plinkysynth/plinky_public/sw/emu/plinkycenter.png

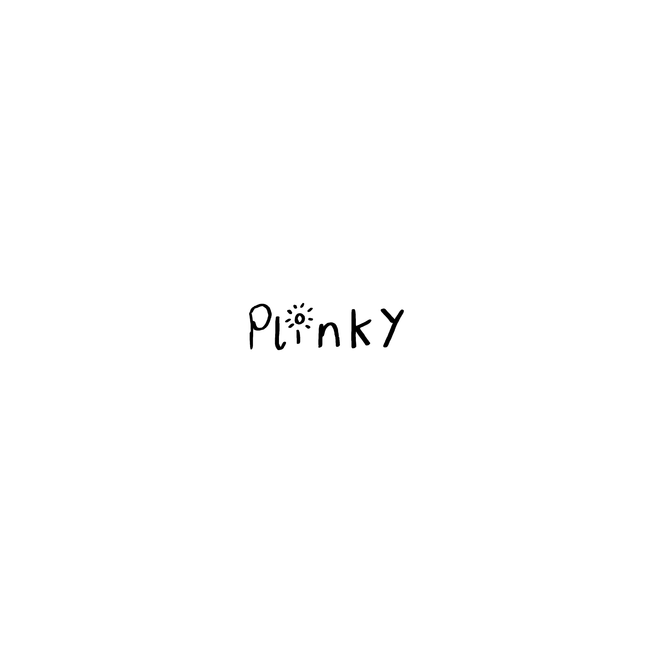
sw/emu/plinkycenter.png
