plinkysynth/plinky_public/sw/emu/plinkydots.png

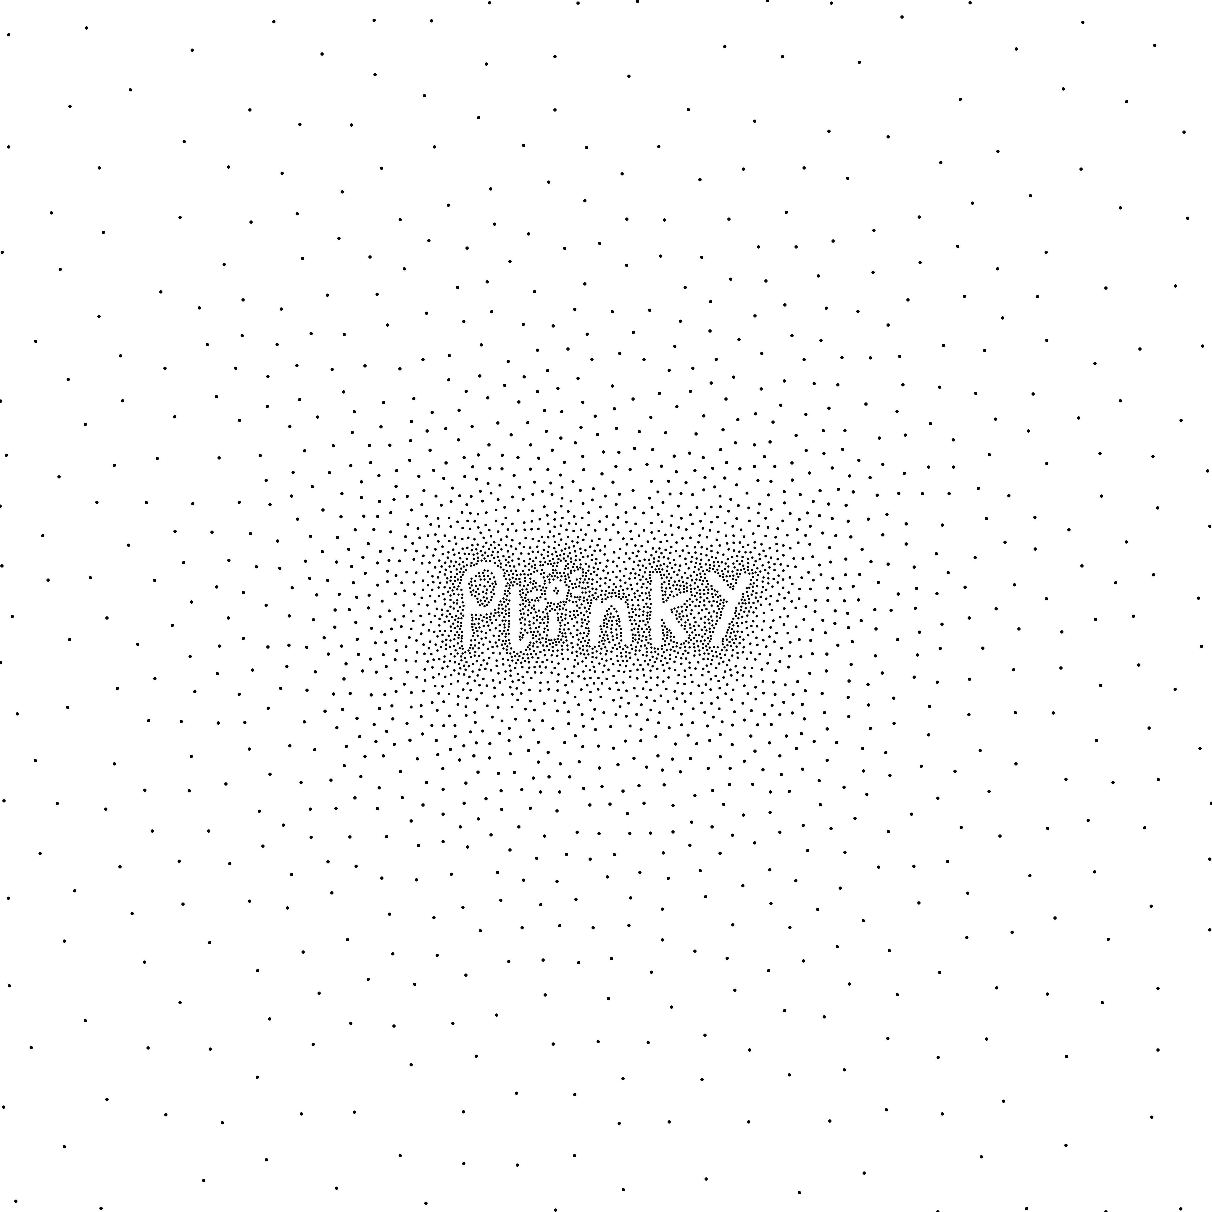
sw/emu/plinkydots.png
