plinkysynth/plinky_public/sw/Core/Src/rand.h

//for j in range(1024):
//  for i in range(64): print(floor(random()*256), end=",")
//  print(" ")
const static u8 rndtab[65536]={
35,243,172,132,46,238,146,27,168,203,208,248,161,108,65,133,225,64,156,212,17,118,12,166,39,9,193,252,196,140,142,141,117,42,28,207,34,26,6,163,206,85,198,204,146,183,76,104,88,250,131,183,165,199,130,209,92,19,103,181,151,198,202,176,
101,220,127,127,235,227,75,237,2,6,141,98,34,221,191,17,177,227,3,111,49,157,106,96,122,251,120,206,197,236,175,132,35,98,35,248,20,193,196,253,25,48,147,241,55,147,119,41,121,103,220,185,177,153,115,48,118,86,246,99,32,112,102,252,
149,72,192,174,2,197,184,136,180,126,4,61,247,112,68,243,146,3,47,0,195,55,48,135,64,215,122,155,6,203,44,49,142,196,99,18,207,223,106,167,67,28,230,237,20,240,34,218,200,84,101,87,73,17,227,70,204,130,178,19,127,252,243,191,
172,158,160,196,148,49,220,85,155,48,104,140,170,27,237,165,212,49,193,68,101,100,109,107,53,54,189,84,2,75,10,255,158,41,94,231,135,52,57,24,151,128,201,76,98,122,45,84,156,32,84,12,216,17,214,89,152,118,157,29,203,60,161,255,
136,169,204,158,255,111,164,47,69,193,126,234,58,68,188,179,10,251,78,182,96,211,13,142,169,132,87,255,31,72,91,137,98,219,165,106,244,171,223,191,160,124,159,80,18,73,119,189,0,35,145,19,202,13,101,94,233,9,16,23,84,35,134,84,
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
136,64,213,102,98,235,86,199,145,164,50,143,65,114,117,60,82,147,7,19,90,80,53,248,254,169,85,68,3,78,29,211,16,95,59,234,129,25,241,25,193,7,244,248,76,235,140,130,25,32,182,119,187,145,40,221,117,244,152,62,106,119,165,97,
130,74,192,129,239,233,243,116,252,127,149,220,67,14,162,77,242,240,167,41,234,85,177,85,228,226,97,255,0,66,43,216,149,55,187,240,4,208,29,141,176,219,250,198,87,188,216,192,84,215,92,180,146,72,192,53,26,50,101,35,145,58,1,213,
237,243,162,154,214,234,244,200,149,87,29,198,166,12,27,207,173,204,108,184,230,124,213,165,173,52,83,31,15,82,31,2,134,81,44,44,125,122,43,46,254,134,119,192,111,127,60,252,168,67,26,138,99,37,211,239,28,145,82,120,136,80,176,80,
36,105,209,234,29,73,100,238,198,92,41,168,138,132,78,36,4,65,241,214,214,236,102,249,191,2,178,156,147,164,195,2,97,0,255,252,129,52,202,20,221,12,80,196,226,71,230,248,138,33,86,137,160,3,76,129,195,146,10,145,120,33,141,162,
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
};
