plinkysynth/plinky_public/sw/Core/Src/sigmoid.h

/*
 * tanh curve plus a bit of even distortion, effectively applies a gain of 2 near the origin, 1/2 at the extremes ie peaks at +-16384
 	for (int i=0;i<65536;++i) {
		short x=(short)i;
		float fx=x/32768.f*4.f;
		float hy=tanh(fx)+tanh(fx*fx*0.0006f); // bit of even distortion too
		int y=0.5f*32500.f*hy;
		DebugLog("%d,",y); 	if ((x&1023)==1023) DebugLog("\n");
	}
 *
 */
const static s16 sigmoid[65536]={
0,1,3,5,7,9,11,13,15,17,19,21,23,25,27,29,31,33,35,37,39,41,43,45,47,49,51,53,55,57,59,61,63,65,67,69,71,73,75,77,79,81,83,85,87,89,91,93,95,97,99,101,103,105,107,109,111,113,115,117,119,121,122,124,126,128,130,132,134,136,138,140,142,144,146,148,150,152,154,156,158,160,162,164,166,168,170,172,174,176,178,180,182,184,186,188,190,192,194,196,198,200,202,204,206,208,210,212,214,216,218,220,222,224,226,228,230,232,234,236,238,240,241,243,245,247,249,251,253,255,257,259,261,263,265,267,269,271,273,275,277,279,281,283,285,287,289,291,293,295,297,299,301,303,305,307,309,311,313,315,317,319,321,323,325,327,329,331,333,335,337,339,341,343,345,347,349,351,353,355,357,358,360,362,364,366,368,370,372,374,376,378,380,382,384,386,388,390,392,394,396,398,400,402,404,406,408,410,412,414,416,418,420,422,424,426,428,430,432,434,436,438,440,442,444,446,448,450,452,454,456,458,460,462,464,466,468,470,471,473,475,477,479,481,483,485,487,489,491,493,495,497,499,501,503,505,507,509,511,513,515,517,519,521,523,525,527,529,531,533,535,537,539,541,543,545,547,549,551,553,555,557,559,561,563,565,567,569,571,573,575,577,578,580,582,584,586,588,590,592,594,596,598,600,602,604,606,608,610,612,614,616,618,620,622,624,626,628,630,632,634,636,638,640,642,644,646,648,650,652,654,656,658,660,662,664,666,668,670,672,674,676,678,680,681,683,685,687,689,691,693,695,697,699,701,703,705,707,709,711,713,715,717,719,721,723,725,727,729,731,733,735,737,739,741,743,745,747,749,751,753,755,757,759,761,763,765,767,769,7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
11421,11422,11423,11424,11425,11426,11427,11428,11429,11430,11431,11432,11433,11434,11435,11436,11437,11438,11439,11440,11441,11442,11443,11444,
11445,11446,11447,11448,11449,11450,11451,11452,11453,11454,11455,11456,11457,11458,11459,11460,11461,11462,11463,11464,11465,11466,11467,11468,11469,11470,11471,11472,11473,11474,11475,11476,11477,11478,11479,11480,11481,11482,11483,11484,11485,11486,11487,11488,11489,11490,11491,11492,11493,11494,11495,11496,11497,11498,11499,11500,11501,11502,11503,11504,11505,11506,11507,11508,11509,11510,11511,11512,11513,11514,11515,11516,11517,11518,11519,11520,11521,11522,11523,11524,11525,11526,11527,11528,11529,11530,11531,11532,11533,11534,11535,11536,11537,11538,11539,11540,11541,11542,11543,11544,11545,11546,11547,11548,11549,11550,11551,11552,11553,11554,11555,11556,11557,11558,11559,11560,11561,11562,11563,11564,11565,11566,11567,11567,11568,11569,11570,11571,11572,11573,11574,11575,11576,11577,11578,11579,11580,11581,11582,11583,11584,11585,11586,11587,11588,11589,11590,11591,11592,11593,11594,11595,11596,11597,11598,11599,11600,11601,11602,11603,11604,11605,11606,11607,11608,11609,11610,11611,11612,11612,11613,11614,11615,11616,11617,11618,11619,11620,11621,11622,11623,11624,11625,11626,11627,11628,11629,11630,11631,11632,11633,11634,11635,11636,11637,11638,11639,11640,11641,11642,11643,11644,11645,11645,11646,11647,11648,11649,11650,11651,11652,11653,11654,11655,11656,11657,11658,11659,11660,11661,11662,11663,11664,11665,11666,11667,11668,11669,11670,11671,11672,11673,11674,11674,11675,11676,11677,11678,11679,11680,11681,11682,11683,11684,11685,11686,11687,11688,11689,11690,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
12365,12366,12367,12368,12368,12369,12370,12371,12372,12373,12373,12374,12375,12376,12377,12378,12378,12379,12380,12381,12382,12383,12383,12384,
12385,12386,12387,12388,12388,12389,12390,12391,12392,12393,12394,12394,12395,12396,12397,12398,12399,12399,12400,12401,12402,12403,12403,12404,12405,12406,12407,12408,12408,12409,12410,12411,12412,12413,12413,12414,12415,12416,12417,12418,12418,12419,12420,12421,12422,12423,12423,12424,12425,12426,12427,12428,12428,12429,12430,12431,12432,12433,12433,12434,12435,12436,12437,12437,12438,12439,12440,12441,12442,12442,12443,12444,12445,12446,12447,12447,12448,12449,12450,12451,12451,12452,12453,12454,12455,12456,12456,12457,12458,12459,12460,12461,12461,12462,12463,12464,12465,12465,12466,12467,12468,12469,12470,12470,12471,12472,12473,12474,12474,12475,12476,12477,12478,12479,12479,12480,12481,12482,12483,12483,12484,12485,12486,12487,12488,12488,12489,12490,12491,12492,12492,12493,12494,12495,12496,12497,12497,12498,12499,12500,12501,12501,12502,12503,12504,12505,12505,12506,12507,12508,12509,12510,12510,12511,12512,12513,12514,12514,12515,12516,12517,12518,12518,12519,12520,12521,12522,12523,12523,12524,12525,12526,12527,12527,12528,12529,12530,12531,12531,12532,12533,12534,12535,12535,12536,12537,12538,12539,12540,12540,12541,12542,12543,12544,12544,12545,12546,12547,12548,12548,12549,12550,12551,12552,12552,12553,12554,12555,12556,12556,12557,12558,12559,12560,12560,12561,12562,12563,12564,12564,12565,12566,12567,12568,12568,12569,12570,12571,12572,12572,12573,12574,12575,12576,12576,12577,12578,12579,12580,12580,12581,12582,12583,12584,12584,12585,12586,12587,12588,12588,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
13146,13147,13148,13149,13149,13150,13151,13151,13152,13153,13153,13154,13155,13155,13156,13157,13157,13158,13159,13160,13160,13161,13162,13162,
13163,13164,13164,13165,13166,13166,13167,13168,13168,13169,13170,13171,13171,13172,13173,13173,13174,13175,13175,13176,13177,13177,13178,13179,13179,13180,13181,13181,13182,13183,13184,13184,13185,13186,13186,13187,13188,13188,13189,13190,13190,13191,13192,13192,13193,13194,13194,13195,13196,13196,13197,13198,13199,13199,13200,13201,13201,13202,13203,13203,13204,13205,13205,13206,13207,13207,13208,13209,13209,13210,13211,13211,13212,13213,13213,13214,13215,13215,13216,13217,13218,13218,13219,13220,13220,13221,13222,13222,13223,13224,13224,13225,13226,13226,13227,13228,13228,13229,13230,13230,13231,13232,13232,13233,13234,13234,13235,13236,13236,13237,13238,13238,13239,13240,13240,13241,13242,13242,13243,13244,13244,13245,13246,13246,13247,13248,13248,13249,13250,13251,13251,13252,13253,13253,13254,13255,13255,13256,13257,13257,13258,13259,13259,13260,13261,13261,13262,13263,13263,13264,13265,13265,13266,13267,13267,13268,13269,13269,13270,13271,13271,13272,13273,13273,13274,13275,13275,13276,13277,13277,13278,13279,13279,13280,13281,13281,13282,13283,13283,13284,13284,13285,13286,13286,13287,13288,13288,13289,13290,13290,13291,13292,13292,13293,13294,13294,13295,13296,13296,13297,13298,13298,13299,13300,13300,13301,13302,13302,13303,13304,13304,13305,13306,13306,13307,13308,13308,13309,13310,13310,13311,13312,13312,13313,13314,13314,13315,13316,13316,13317,13317,13318,13319,13319,13320,13321,13321,13322,13323,13323,13324,13325,13325,13326,13327,13327,13328,13329,13329,13330,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
13786,13786,13787,13788,13788,13789,13789,13790,13790,13791,13792,13792,13793,13793,13794,13794,13795,13795,13796,13797,13797,13798,13798,13799,
13799,13800,13800,13801,13802,13802,13803,13803,13804,13804,13805,13805,13806,13807,13807,13808,13808,13809,13809,13810,13811,13811,13812,13812,13813,13813,13814,13814,13815,13816,13816,13817,13817,13818,13818,13819,13819,13820,13821,13821,13822,13822,13823,13823,13824,13824,13825,13825,13826,13827,13827,13828,13828,13829,13829,13830,13830,13831,13832,13832,13833,13833,13834,13834,13835,13835,13836,13837,13837,13838,13838,13839,13839,13840,13840,13841,13842,13842,13843,13843,13844,13844,13845,13845,13846,13846,13847,13848,13848,13849,13849,13850,13850,13851,13851,13852,13853,13853,13854,13854,13855,13855,13856,13856,13857,13857,13858,13859,13859,13860,13860,13861,13861,13862,13862,13863,13863,13864,13865,13865,13866,13866,13867,13867,13868,13868,13869,13869,13870,13871,13871,13872,13872,13873,13873,13874,13874,13875,13875,13876,13877,13877,13878,13878,13879,13879,13880,13880,13881,13881,13882,13882,13883,13884,13884,13885,13885,13886,13886,13887,13887,13888,13888,13889,13890,13890,13891,13891,13892,13892,13893,13893,13894,13894,13895,13895,13896,13897,13897,13898,13898,13899,13899,13900,13900,13901,13901,13902,13902,13903,13904,13904,13905,13905,13906,13906,13907,13907,13908,13908,13909,13909,13910,13911,13911,13912,13912,13913,13913,13914,13914,13915,13915,13916,13916,13917,13917,13918,13919,13919,13920,13920,13921,13921,13922,13922,13923,13923,13924,13924,13925,13925,13926,13927,13927,13928,13928,13929,13929,13930,13930,13931,13931,13932,13932,13933,13933,13934,13935,13935,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
14304,14305,14305,14306,14306,14307,14307,14307,14308,14308,14309,14309,14310,14310,14311,14311,14312,14312,14312,14313,14313,14314,14314,14315,
14315,14316,14316,14316,14317,14317,14318,14318,14319,14319,14320,14320,14321,14321,14321,14322,14322,14323,14323,14324,14324,14325,14325,14325,14326,14326,14327,14327,14328,14328,14329,14329,14330,14330,14330,14331,14331,14332,14332,14333,14333,14334,14334,14334,14335,14335,14336,14336,14337,14337,14338,14338,14338,14339,14339,14340,14340,14341,14341,14342,14342,14342,14343,14343,14344,14344,14345,14345,14346,14346,14346,14347,14347,14348,14348,14349,14349,14350,14350,14350,14351,14351,14352,14352,14353,14353,14354,14354,14354,14355,14355,14356,14356,14357,14357,14358,14358,14358,14359,14359,14360,14360,14361,14361,14362,14362,14362,14363,14363,14364,14364,14365,14365,14366,14366,14366,14367,14367,14368,14368,14369,14369,14369,14370,14370,14371,14371,14372,14372,14373,14373,14373,14374,14374,14375,14375,14376,14376,14377,14377,14377,14378,14378,14379,14379,14380,14380,14380,14381,14381,14382,14382,14383,14383,14384,14384,14384,14385,14385,14386,14386,14387,14387,14387,14388,14388,14389,14389,14390,14390,14390,14391,14391,14392,14392,14393,14393,14394,14394,14394,14395,14395,14396,14396,14397,14397,14397,14398,14398,14399,14399,14400,14400,14400,14401,14401,14402,14402,14403,14403,14403,14404,14404,14405,14405,14406,14406,14407,14407,14407,14408,14408,14409,14409,14410,14410,14410,14411,14411,14412,14412,14413,14413,14413,14414,14414,14415,14415,14416,14416,14416,14417,14417,14418,14418,14419,14419,14419,14420,14420,14421,14421,14422,14422,14422,14423,14423,14424,14424,14425,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
14721,14722,14722,14722,14723,14723,14724,14724,14724,14725,14725,14725,14726,14726,14726,14727,14727,14728,14728,14728,14729,14729,14729,14730,
14730,14730,14731,14731,14732,14732,14732,14733,14733,14733,14734,14734,14734,14735,14735,14736,14736,14736,14737,14737,14737,14738,14738,14738,14739,14739,14739,14740,14740,14741,14741,14741,14742,14742,14742,14743,14743,14743,14744,14744,14745,14745,14745,14746,14746,14746,14747,14747,14747,14748,14748,14748,14749,14749,14750,14750,14750,14751,14751,14751,14752,14752,14752,14753,14753,14753,14754,14754,14755,14755,14755,14756,14756,14756,14757,14757,14757,14758,14758,14758,14759,14759,14760,14760,14760,14761,14761,14761,14762,14762,14762,14763,14763,14763,14764,14764,14764,14765,14765,14766,14766,14766,14767,14767,14767,14768,14768,14768,14769,14769,14769,14770,14770,14771,14771,14771,14772,14772,14772,14773,14773,14773,14774,14774,14774,14775,14775,14775,14776,14776,14776,14777,14777,14778,14778,14778,14779,14779,14779,14780,14780,14780,14781,14781,14781,14782,14782,14782,14783,14783,14784,14784,14784,14785,14785,14785,14786,14786,14786,14787,14787,14787,14788,14788,14788,14789,14789,14789,14790,14790,14791,14791,14791,14792,14792,14792,14793,14793,14793,14794,14794,14794,14795,14795,14795,14796,14796,14796,14797,14797,14797,14798,14798,14799,14799,14799,14800,14800,14800,14801,14801,14801,14802,14802,14802,14803,14803,14803,14804,14804,14804,14805,14805,14805,14806,14806,14806,14807,14807,14808,14808,14808,14809,14809,14809,14810,14810,14810,14811,14811,14811,14812,14812,14812,14813,14813,14813,14814,14814,14814,14815,14815,14815,14816,14816,14816,14817,14817,14817,14818,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
15055,15055,15056,15056,15056,15057,15057,15057,15057,15058,15058,15058,15059,15059,15059,15060,15060,15060,15060,15061,15061,15061,15062,15062,
15062,15062,15063,15063,15063,15064,15064,15064,15064,15065,15065,15065,15066,15066,15066,15066,15067,15067,15067,15068,15068,15068,15068,15069,15069,15069,15070,15070,15070,15070,15071,15071,15071,15072,15072,15072,15072,15073,15073,15073,15074,15074,15074,15074,15075,15075,15075,15076,15076,15076,15076,15077,15077,15077,15078,15078,15078,15078,15079,15079,15079,15080,15080,15080,15080,15081,15081,15081,15082,15082,15082,15082,15083,15083,15083,15084,15084,15084,15084,15085,15085,15085,15086,15086,15086,15086,15087,15087,15087,15088,15088,15088,15088,15089,15089,15089,15090,15090,15090,15090,15091,15091,15091,15092,15092,15092,15092,15093,15093,15093,15094,15094,15094,15094,15095,15095,15095,15095,15096,15096,15096,15097,15097,15097,15097,15098,15098,15098,15099,15099,15099,15099,15100,15100,15100,15101,15101,15101,15101,15102,15102,15102,15103,15103,15103,15103,15104,15104,15104,15104,15105,15105,15105,15106,15106,15106,15106,15107,15107,15107,15108,15108,15108,15108,15109,15109,15109,15109,15110,15110,15110,15111,15111,15111,15111,15112,15112,15112,15113,15113,15113,15113,15114,15114,15114,15115,15115,15115,15115,15116,15116,15116,15116,15117,15117,15117,15118,15118,15118,15118,15119,15119,15119,15119,15120,15120,15120,15121,15121,15121,15121,15122,15122,15122,15123,15123,15123,15123,15124,15124,15124,15124,15125,15125,15125,15126,15126,15126,15126,15127,15127,15127,15127,15128,15128,15128,15129,15129,15129,15129,15130,15130,15130,15130,15131,15131,15131,15132,15132,15132,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
15321,15321,15322,15322,15322,15322,15323,15323,15323,15323,15323,15324,15324,15324,15324,15325,15325,15325,15325,15326,15326,15326,15326,15326,
15327,15327,15327,15327,15328,15328,15328,15328,15329,15329,15329,15329,15329,15330,15330,15330,15330,15331,15331,15331,15331,15332,15332,15332,15332,15332,15333,15333,15333,15333,15334,15334,15334,15334,15335,15335,15335,15335,15335,15336,15336,15336,15336,15337,15337,15337,15337,15337,15338,15338,15338,15338,15339,15339,15339,15339,15340,15340,15340,15340,15340,15341,15341,15341,15341,15342,15342,15342,15342,15342,15343,15343,15343,15343,15344,15344,15344,15344,15344,15345,15345,15345,15345,15346,15346,15346,15346,15347,15347,15347,15347,15347,15348,15348,15348,15348,15349,15349,15349,15349,15349,15350,15350,15350,15350,15351,15351,15351,15351,15351,15352,15352,15352,15352,15353,15353,15353,15353,15353,15354,15354,15354,15354,15355,15355,15355,15355,15356,15356,15356,15356,15356,15357,15357,15357,15357,15358,15358,15358,15358,15358,15359,15359,15359,15359,15360,15360,15360,15360,15360,15361,15361,15361,15361,15362,15362,15362,15362,15362,15363,15363,15363,15363,15364,15364,15364,15364,15364,15365,15365,15365,15365,15366,15366,15366,15366,15366,15367,15367,15367,15367,15367,15368,15368,15368,15368,15369,15369,15369,15369,15369,15370,15370,15370,15370,15371,15371,15371,15371,15371,15372,15372,15372,15372,15373,15373,15373,15373,15373,15374,15374,15374,15374,15375,15375,15375,15375,15375,15376,15376,15376,15376,15377,15377,15377,15377,15377,15378,15378,15378,15378,15378,15379,15379,15379,15379,15380,15380,15380,15380,15380,15381,15381,15381,15381,15382,15382,15382,15382,15382,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
15533,15533,15533,15533,15533,15534,15534,15534,15534,15534,15534,15535,15535,15535,15535,15535,15536,15536,15536,15536,15536,15536,15537,15537,
15537,15537,15537,15538,15538,15538,15538,15538,15538,15539,15539,15539,15539,15539,15540,15540,15540,15540,15540,15540,15541,15541,15541,15541,15541,15542,15542,15542,15542,15542,15542,15543,15543,15543,15543,15543,15544,15544,15544,15544,15544,15544,15545,15545,15545,15545,15545,15546,15546,15546,15546,15546,15546,15547,15547,15547,15547,15547,15548,15548,15548,15548,15548,15548,15549,15549,15549,15549,15549,15550,15550,15550,15550,15550,15550,15551,15551,15551,15551,15551,15551,15552,15552,15552,15552,15552,15553,15553,15553,15553,15553,15553,15554,15554,15554,15554,15554,15555,15555,15555,15555,15555,15555,15556,15556,15556,15556,15556,15556,15557,15557,15557,15557,15557,15558,15558,15558,15558,15558,15558,15559,15559,15559,15559,15559,15560,15560,15560,15560,15560,15560,15561,15561,15561,15561,15561,15561,15562,15562,15562,15562,15562,15563,15563,15563,15563,15563,15563,15564,15564,15564,15564,15564,15564,15565,15565,15565,15565,15565,15566,15566,15566,15566,15566,15566,15567,15567,15567,15567,15567,15567,15568,15568,15568,15568,15568,15569,15569,15569,15569,15569,15569,15570,15570,15570,15570,15570,15570,15571,15571,15571,15571,15571,15571,15572,15572,15572,15572,15572,15573,15573,15573,15573,15573,15573,15574,15574,15574,15574,15574,15574,15575,15575,15575,15575,15575,15576,15576,15576,15576,15576,15576,15577,15577,15577,15577,15577,15577,15578,15578,15578,15578,15578,15578,15579,15579,15579,15579,15579,15579,15580,15580,15580,15580,15580,15581,15581,15581,15581,15581,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
15700,15701,15701,15701,15701,15701,15701,15701,15702,15702,15702,15702,15702,15702,15702,15703,15703,15703,15703,15703,15703,15704,15704,15704,
15704,15704,15704,15704,15705,15705,15705,15705,15705,15705,15705,15706,15706,15706,15706,15706,15706,15706,15707,15707,15707,15707,15707,15707,15707,15708,15708,15708,15708,15708,15708,15708,15709,15709,15709,15709,15709,15709,15709,15710,15710,15710,15710,15710,15710,15710,15711,15711,15711,15711,15711,15711,15711,15712,15712,15712,15712,15712,15712,15712,15713,15713,15713,15713,15713,15713,15713,15714,15714,15714,15714,15714,15714,15714,15715,15715,15715,15715,15715,15715,15715,15716,15716,15716,15716,15716,15716,15716,15717,15717,15717,15717,15717,15717,15717,15718,15718,15718,15718,15718,15718,15718,15719,15719,15719,15719,15719,15719,15719,15720,15720,15720,15720,15720,15720,15720,15721,15721,15721,15721,15721,15721,15721,15722,15722,15722,15722,15722,15722,15722,15723,15723,15723,15723,15723,15723,15723,15723,15724,15724,15724,15724,15724,15724,15724,15725,15725,15725,15725,15725,15725,15725,15726,15726,15726,15726,15726,15726,15726,15727,15727,15727,15727,15727,15727,15727,15728,15728,15728,15728,15728,15728,15728,15729,15729,15729,15729,15729,15729,15729,15730,15730,15730,15730,15730,15730,15730,15730,15731,15731,15731,15731,15731,15731,15731,15732,15732,15732,15732,15732,15732,15732,15733,15733,15733,15733,15733,15733,15733,15734,15734,15734,15734,15734,15734,15734,15734,15735,15735,15735,15735,15735,15735,15735,15736,15736,15736,15736,15736,15736,15736,15737,15737,15737,15737,15737,15737,15737,15738,15738,15738,15738,15738,15738,15738,15738,15739,15739,15739,15739,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
15834,15834,15834,15834,15834,15834,15834,15834,15835,15835,15835,15835,15835,15835,15835,15835,15836,15836,15836,15836,15836,15836,15836,15836,
15836,15837,15837,15837,15837,15837,15837,15837,15837,15837,15838,15838,15838,15838,15838,15838,15838,15838,15839,15839,15839,15839,15839,15839,15839,15839,15839,15840,15840,15840,15840,15840,15840,15840,15840,15840,15841,15841,15841,15841,15841,15841,15841,15841,15841,15842,15842,15842,15842,15842,15842,15842,15842,15843,15843,15843,15843,15843,15843,15843,15843,15843,15844,15844,15844,15844,15844,15844,15844,15844,15844,15845,15845,15845,15845,15845,15845,15845,15845,15845,15846,15846,15846,15846,15846,15846,15846,15846,15846,15847,15847,15847,15847,15847,15847,15847,15847,15848,15848,15848,15848,15848,15848,15848,15848,15848,15849,15849,15849,15849,15849,15849,15849,15849,15849,15850,15850,15850,15850,15850,15850,15850,15850,15850,15851,15851,15851,15851,15851,15851,15851,15851,15851,15852,15852,15852,15852,15852,15852,15852,15852,15852,15853,15853,15853,15853,15853,15853,15853,15853,15853,15854,15854,15854,15854,15854,15854,15854,15854,15854,15855,15855,15855,15855,15855,15855,15855,15855,15855,15856,15856,15856,15856,15856,15856,15856,15856,15856,15857,15857,15857,15857,15857,15857,15857,15857,15857,15858,15858,15858,15858,15858,15858,15858,15858,15858,15859,15859,15859,15859,15859,15859,15859,15859,15859,15860,15860,15860,15860,15860,15860,15860,15860,15860,15861,15861,15861,15861,15861,15861,15861,15861,15861,15861,15862,15862,15862,15862,15862,15862,15862,15862,15862,15863,15863,15863,15863,15863,15863,15863,15863,15863,15864,15864,15864,15864,15864,15864,15864,15864,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
15940,15940,15940,15940,15940,15940,15940,15940,15940,15940,15940,15941,15941,15941,15941,15941,15941,15941,15941,15941,15941,15942,15942,15942,
15942,15942,15942,15942,15942,15942,15942,15942,15943,15943,15943,15943,15943,15943,15943,15943,15943,15943,15943,15944,15944,15944,15944,15944,15944,15944,15944,15944,15944,15944,15945,15945,15945,15945,15945,15945,15945,15945,15945,15945,15945,15946,15946,15946,15946,15946,15946,15946,15946,15946,15946,15946,15947,15947,15947,15947,15947,15947,15947,15947,15947,15947,15947,15948,15948,15948,15948,15948,15948,15948,15948,15948,15948,15948,15949,15949,15949,15949,15949,15949,15949,15949,15949,15949,15949,15949,15950,15950,15950,15950,15950,15950,15950,15950,15950,15950,15950,15951,15951,15951,15951,15951,15951,15951,15951,15951,15951,15951,15952,15952,15952,15952,15952,15952,15952,15952,15952,15952,15952,15953,15953,15953,15953,15953,15953,15953,15953,15953,15953,15953,15954,15954,15954,15954,15954,15954,15954,15954,15954,15954,15954,15954,15955,15955,15955,15955,15955,15955,15955,15955,15955,15955,15955,15956,15956,15956,15956,15956,15956,15956,15956,15956,15956,15956,15957,15957,15957,15957,15957,15957,15957,15957,15957,15957,15957,15958,15958,15958,15958,15958,15958,15958,15958,15958,15958,15958,15958,15959,15959,15959,15959,15959,15959,15959,15959,15959,15959,15959,15960,15960,15960,15960,15960,15960,15960,15960,15960,15960,15960,15960,15961,15961,15961,15961,15961,15961,15961,15961,15961,15961,15961,15962,15962,15962,15962,15962,15962,15962,15962,15962,15962,15962,15962,15963,15963,15963,15963,15963,15963,15963,15963,15963,15963,15963,15964,15964,15964,15964,15964,15964,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
16024,16024,16024,16024,16024,16024,16024,16024,16025,16025,16025,16025,16025,16025,16025,16025,16025,16025,16025,16025,16025,16026,16026,16026,
16026,16026,16026,16026,16026,16026,16026,16026,16026,16026,16026,16027,16027,16027,16027,16027,16027,16027,16027,16027,16027,16027,16027,16027,16027,16028,16028,16028,16028,16028,16028,16028,16028,16028,16028,16028,16028,16028,16028,16029,16029,16029,16029,16029,16029,16029,16029,16029,16029,16029,16029,16029,16030,16030,16030,16030,16030,16030,16030,16030,16030,16030,16030,16030,16030,16030,16031,16031,16031,16031,16031,16031,16031,16031,16031,16031,16031,16031,16031,16031,16032,16032,16032,16032,16032,16032,16032,16032,16032,16032,16032,16032,16032,16032,16033,16033,16033,16033,16033,16033,16033,16033,16033,16033,16033,16033,16033,16033,16034,16034,16034,16034,16034,16034,16034,16034,16034,16034,16034,16034,16034,16034,16035,16035,16035,16035,16035,16035,16035,16035,16035,16035,16035,16035,16035,16035,16036,16036,16036,16036,16036,16036,16036,16036,16036,16036,16036,16036,16036,16036,16037,16037,16037,16037,16037,16037,16037,16037,16037,16037,16037,16037,16037,16037,16038,16038,16038,16038,16038,16038,16038,16038,16038,16038,16038,16038,16038,16038,16038,16039,16039,16039,16039,16039,16039,16039,16039,16039,16039,16039,16039,16039,16039,16040,16040,16040,16040,16040,16040,16040,16040,16040,16040,16040,16040,16040,16040,16041,16041,16041,16041,16041,16041,16041,16041,16041,16041,16041,16041,16041,16041,16042,16042,16042,16042,16042,16042,16042,16042,16042,16042,16042,16042,16042,16042,16042,16043,16043,16043,16043,16043,16043,16043,16043,16043,16043,16043,16043,16043,16043,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
16092,16092,16092,16092,16092,16092,16092,16092,16092,16092,16092,16092,16092,16092,16092,16092,16092,16093,16093,16093,16093,16093,16093,16093,
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
