plinkysynth/plinky_public/sw/Core/Src/wavetable.h

// generated for WT_LAST 17 WAVETABLE_SIZE 1031
const short wavetable[17][1031]={
	// Saw
	{-585,-18796,-15405,-16407,-16166,-15980,-16054,-15925,-15872,-15808,-15743,-15680,-15615,-15552,-15488,-15424,-15359,-15296,-15231,-15168,-15104,-15039,-14975,-14911,-14848,-14783,-14720,-14655,-14591,-14527,-14464,-14400,-14335,-14272,-14208,-14143,-14080,-14015,-13951,-13888,-13824,-13760,-13695,-13631,-13567,-13503,-13439,-13375,-13311,-13248,-13183,-13119,-13056,-12992,-12927,-12863,-12800,-12736,-12671,-12607,-12543,-12479,-12415,-12352,-12288,-12223,-12160,-12096,-12032,-11968,-11903,-11839,-11775,-11712,-11648,-11583,-11519,-11456,-11391,-11327,-11263,-11199,-11135,-11072,-11007,-10943,-10880,-10815,-10751,-10688,-10624,-10559,-10495,-10432,-10368,-10303,-10239,-10175,-10112,-10047,-9984,-9920,-9856,-9792,-9728,-9664,-9599,-9536,-9472,-9408,-9344,-9280,-9215,-9151,-9087,-9023,-8959,-8896,-8831,-8768,-8704,-8639,-8576,-8512,-8447,-8384,-8319,-8256,-8191,-8127,-8063,-7999,-7935,-7871,-7807,-7743,-7680,-7615,-7551,-7487,-7423,-7359,-7295,-7232,-7167,-7104,-7040,-6976,-6911,-6847,-6783,-6719,-6656,-6592,-6528,-6463,-6399,-6336,-6271,-6207,-6143,-6079,-6016,-5951,-5888,-5823,-5760,-5696,-5632,-5567,-5503,-5439,-5375,-5312,-5247,-5184,-5120,-5055,-4992,-4927,-4863,-4799,-4735,-4671,-4608,-4544,-4480,-4416,-4351,-4288,-4224,-4160,-4096,-4031,-3968,-3904,-3839,-3775,-3711,-3648,-3584,-3519,-3455,-3392,-3327,-3263,-3200,-3135,-3071,-3007,-2943,-2879,-2816,-2751,-2687,-2623,-2560,-2495,-2432,-2367,-2304,-2240,-2175,-2111,-2047,-1984,-1920,-1856,-1791,-1728,-1664,-1599,-1535,-1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
	-585,-16812,-11437,-10455,-8230,-6060,-4150,-2037,0,2037,4147,6076,8190,10528,11328,16948,-585,
	-585,-14775,-7290,-4379,-39,4467,7177,14911,-585,
	-624,-10307,-112,10532,-624,
	-737,225,-737,
	},	// Sin
	{16383,16382,16379,16372,16364,16353,16339,16323,16305,16284,16260,16234,16206,16175,16142,16107,16069,16028,15985,15940,15892,15842,15790,15735,15678,15618,15557,15492,15426,15357,15286,15212,15136,15058,14978,14895,14810,14723,14634,14543,14449,14353,14255,14155,14053,13948,13842,13733,13622,13510,13395,13278,13159,13038,12916,12791,12665,12536,12406,12273,12139,12003,11866,11726,11585,11442,11297,11150,11002,10853,10701,10548,10393,10237,10079,9920,9759,9597,9434,9268,9102,8934,8765,8594,8423,8249,8075,7900,7723,7545,7366,7186,7005,6822,6639,6455,6269,6083,5896,5708,5519,5329,5139,4948,4756,4563,4369,4175,3980,3785,3589,3393,3196,2998,2801,2602,2404,2204,2005,1805,1605,1405,1205,1004,803,603,402,201,0,-201,-402,-603,-803,-1004,-1205,-1405,-1605,-1805,-2005,-2204,-2404,-2602,-2801,-2998,-3196,-3393,-3589,-3785,-3980,-4175,-4369,-4563,-4756,-4948,-5139,-5329,-5519,-5708,-5896,-6083,-6269,-6455,-6639,-6822,-7005,-7186,-7366,-7545,-7723,-7900,-8075,-8249,-8423,-8594,-8765,-8934,-9102,-9268,-9434,-9597,-9759,-9920,-10079,-10237,-10393,-10548,-10701,-10853,-11002,-11150,-11297,-11442,-11585,-11726,-11866,-12003,-12139,-12273,-12406,-12536,-12665,-12791,-12916,-13039,-13159,-13278,-13395,-13510,-13622,-13733,-13842,-13948,-14053,-14155,-14255,-14353,-14449,-14543,-14634,-14723,-14810,-14895,-14978,-15058,-15136,-15212,-15286,-15357,-15426,-15492,-15557,-15618,-15678,-15735,-15790,-15842,-15892,-15940,-15985,-16028,-16069,-16107,-16142,-16175,-16206,-16234,-16260,-16284,-16305,-1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
	16385,16071,15138,13624,11586,9103,6270,3196,0,-3196,-6270,-9103,-11586,-13624,-15138,-16071,-16385,-16071,-15138,-13624,-11586,-9103,-6270,-3196,0,3196,6270,9103,11586,13624,15138,16071,16385,
	16388,15140,11588,6271,0,-6271,-11588,-15140,-16388,-15140,-11588,-6271,0,6271,11588,15140,16388,
	16383,11584,0,-11584,-16383,-11584,0,11584,16383,
	16379,0,-16379,0,16379,
	15394,-15394,15394,
	},	// miunau0
	{-2061,-1002,4577,-2033,2747,3803,2705,12216,6741,15372,11788,13597,14231,10140,13322,6253,7402,4198,-3354,2202,-6738,1265,174,845,10026,5151,14929,11743,14714,14530,12711,13841,9326,9472,6265,2023,4778,-3807,692,-2258,-3150,2847,-2860,6745,2466,6007,4483,-5741,-2214,-8609,-5201,-4935,-5952,-3794,-5978,-4152,-4584,-3208,3021,570,11366,5373,9923,6407,1056,2375,-10371,-6765,-9726,-9736,-6827,-8922,4739,4510,10751,13511,12356,14327,10982,11510,7180,5032,4732,-1318,853,-4634,-7075,-4554,-12005,-3928,-9263,-4711,-2293,-7071,-2943,-13620,-9488,-9754,-10852,-7949,-10429,-8388,-8719,-9166,-4325,-8832,211,-5294,-1029,-484,-6822,-198,-11669,-7005,-11028,-12820,-9122,-11732,-10117,-10686,-11912,-1689,4181,14854,13586,15861,10373,6850,2524,1140,7024,2322,566,0,-6485,-3111,-10445,-10312,-8808,-14518,-6709,-14759,-13042,-11064,-11469,-9570,-10753,-11109,-10371,-11911,-8824,-11504,-6706,-7595,-6169,-1991,-7904,-444,-7735,-4070,-5549,-10745,-6245,-14416,-10574,-11815,-12184,-9938,-12584,-9973,-8786,5864,11655,13046,14013,10384,7633,1119,1799,6368,1563,2230,-3781,-8219,-15105,-16303,-13291,-8952,-9661,-9561,-8989,-9999,-9364,-9845,-9935,-9982,-10755,-9665,-11145,-9124,-10568,-8790,-8024,-9158,-5334,-9916,-6530,-9531,-10502,-8992,-12229,-9695,-10984,-10787,-9829,-11377,-9980,-11273,-10681,-10062,-11277,-7754,-10992,-7381,-9450,-10353,-8482,-12894,-9849,-12295,-11869,-10821,-12534,-10634,-12050,-11505,-11041,-12418,-9680,-12322,-9102,-10438,-10728,-8409,-12648,-9157,-12227,-11783,-10763,-12861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
	-15114,-16484,-15779,-15017,-13237,-10985,-8034,-4617,-2965,-4934,-2463,204,5033,11027,14534,15877,16228,15683,14579,12719,10332,6535,4436,2936,2661,2175,-1995,-8042,-13127,-15335,-16296,-16087,-15114,
	-15375,-16033,-13272,-7795,-3580,-3153,5421,14510,16125,14643,10082,4092,2930,-2021,-12991,-16212,-15375,
	-16138,-12846,-4296,4843,17570,8716,2853,-11687,-16138,
	-15579,-4652,14494,570,-15579,
	-15074,12735,-15074,
	},	// miunau2
	{-2768,-3092,-3325,-3572,-3447,-4209,-3005,-11309,-13565,-10266,-10980,-10104,-9979,-9731,-9567,-9464,-9408,-9392,-9414,-9468,-9549,-9652,-9775,-9912,-10061,-10217,-10372,-10505,-10613,-10680,-10694,-10654,-10563,-10438,-10278,-10096,-9900,-9692,-9472,-9239,-8993,-8735,-8458,-8161,-7834,-7461,-7076,-6522,-6071,-5492,-4069,-5216,5440,16164,10070,12165,10311,10301,9655,9324,8947,8660,8412,8220,8093,8016,7988,8002,8054,8138,8248,8381,8525,8672,8817,8955,9083,9201,9311,9415,9514,9609,9691,9773,9839,9877,10026,9971,9439,9309,9078,8912,8608,8322,8023,7673,7389,7036,6695,6421,6122,5733,5345,4930,4556,4138,3679,3261,2886,2358,1798,1120,390,-449,-1161,-1784,-2164,-2707,-2959,-3506,-3361,-3552,-5232,-15403,-10042,-11317,-9984,-10211,-9883,-9897,-9705,-9718,-9639,-9618,-9629,-9675,-9748,-9846,-9961,-10090,-10232,-10379,-10515,-10629,-10715,-10756,-10746,-10681,-10577,-10440,-10270,-10083,-9883,-9669,-9443,-9206,-8953,-8686,-8400,-8090,-7747,-7370,-6890,-6531,-5630,-5656,-3585,-4724,13538,12342,11457,10925,10415,9795,9470,9037,8737,8456,8235,8071,7966,7908,7897,7926,7990,8083,8201,8338,8482,8627,8768,8901,9024,9137,9244,9346,9443,9532,9618,9678,9766,9768,10017,9506,9188,9029,8860,8657,8384,8066,7746,7386,7019,6645,6345,6037,5757,5450,5100,4693,4256,3850,3413,2987,2627,2164,1777,1259,685,-27,-861,-1692,-2550,-3148,-3517,-3617,-4382,-3184,-11878,-13361,-10464,-10984,-10197,-9941,-9720,-9543,-9455,-9401,-9393,-9420,-9479,-9566,-9676,-9804,-9948,-10103,-10267,-10429,-10569,-10684,-10762,-10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
	-9317,-12331,-13496,-13681,-13888,-12910,-7895,3886,3962,7331,6155,8466,8783,8774,9861,6047,3399,6106,1477,-2537,2397,-1952,-10245,-2140,-3375,-9778,-11758,-13598,-13849,-13772,-13297,-11628,-9317,
	-9951,-13420,-14236,-6563,5866,6726,9073,8315,5397,1140,231,-6508,-3550,-13015,-13196,-13547,-9951,
	-10605,-13879,3989,8432,5743,-1772,-6005,-14437,-10605,
	-14332,1605,5888,-7521,-14332,
	-13015,5017,-13015,
	},	// miunau4
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
